LachlanGit/Arduino_Prop_Bomb/prop_bomb_arduino/random_seed.ino

#include <avr/interrupt.h>
#include <avr/wdt.h>
#include <util/atomic.h>
// The following addresses a problem in version 1.0.5 and earlier of the Arduino IDE
// that prevents randomSeed from working properly.
//        https://github.com/arduino/Arduino/issues/575
#define randomSeed(s) srandom(s)


void CreateTrulyRandomSeed()
{
  seed = 0;
  nrot = 32; // Must be at least 4, but more increased the uniformity of the produced
  // seeds entropy.

  // The following five lines of code turn on the watch dog timer interrupt to create
  // the seed value
  cli();
  MCUSR = 0;
  _WD_CONTROL_REG |= (1 << _WD_CHANGE_BIT) | (1 << WDE);
  _WD_CONTROL_REG = (1 << WDIE);
  sei();

  while (nrot > 0);  // wait here until seed is created

  // The following five lines turn off the watch dog timer interrupt
  cli();
  MCUSR = 0;
  _WD_CONTROL_REG |= (1 << _WD_CHANGE_BIT) | (0 << WDE);
  _WD_CONTROL_REG = (0 << WDIE);
  sei();
}

ISR(WDT_vect)
{
  nrot--;
  seed = seed << 8;
  seed = seed ^ TCNT1L;
}
